enpe/ledterne/media/ledterne-test-display-01.jpg

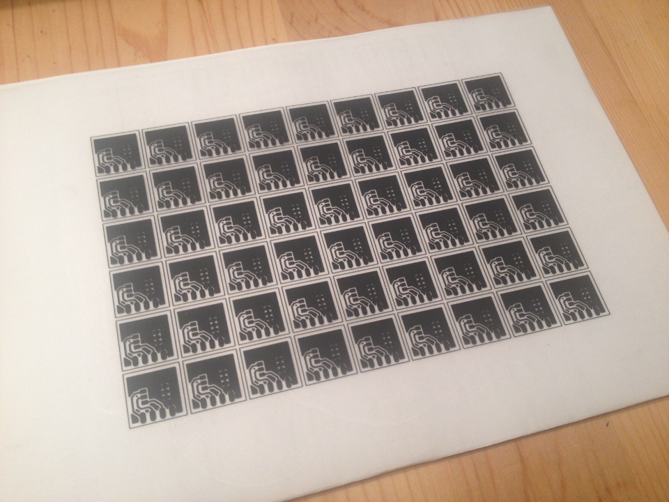
media/ledterne-test-display-01.jpg
