enpe/ledterne/media/ledterne-test-display-03.jpg

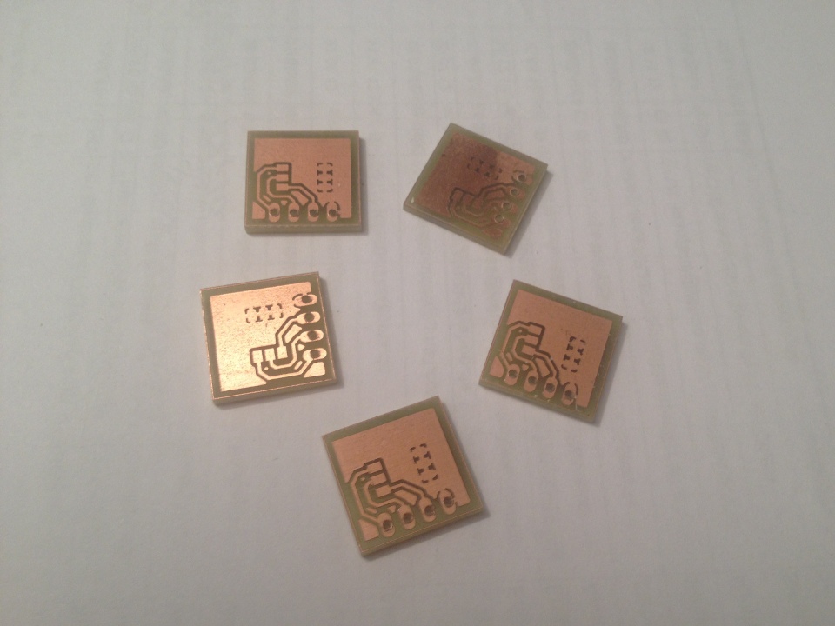
media/ledterne-test-display-03.jpg
