enpe/ledterne/media/ledterne-test-display-06.jpg

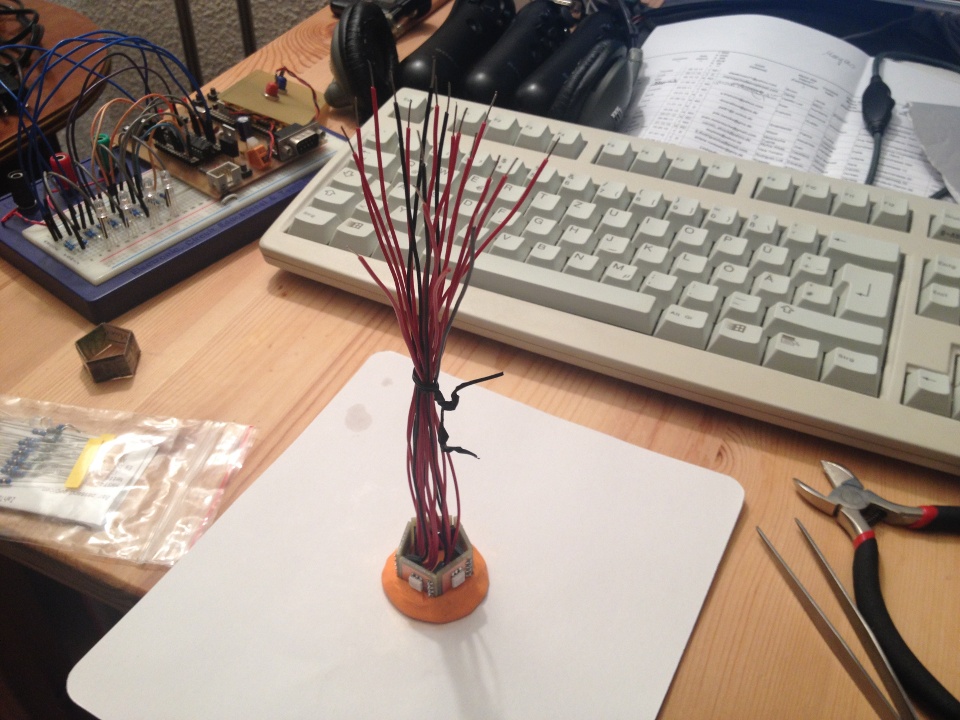
media/ledterne-test-display-06.jpg
