enpe/ledterne/media/ledterne-test-display-07.jpg

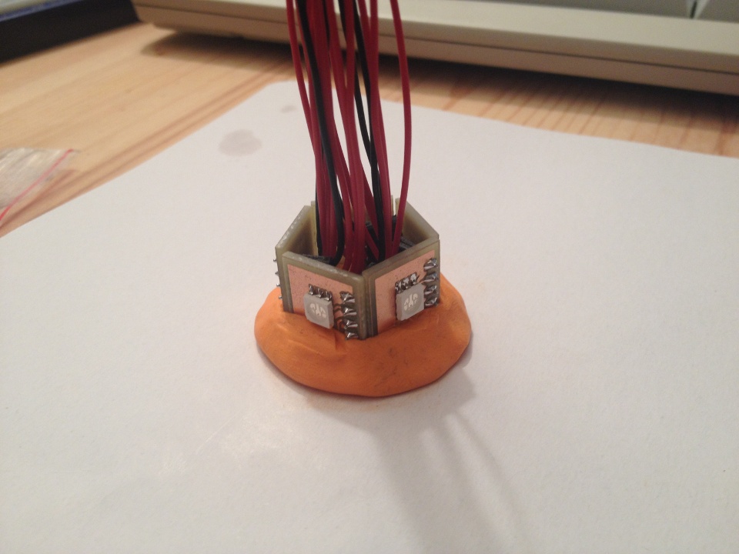
media/ledterne-test-display-07.jpg
