enpe/ledterne/media/ledterne-test-display-08.jpg

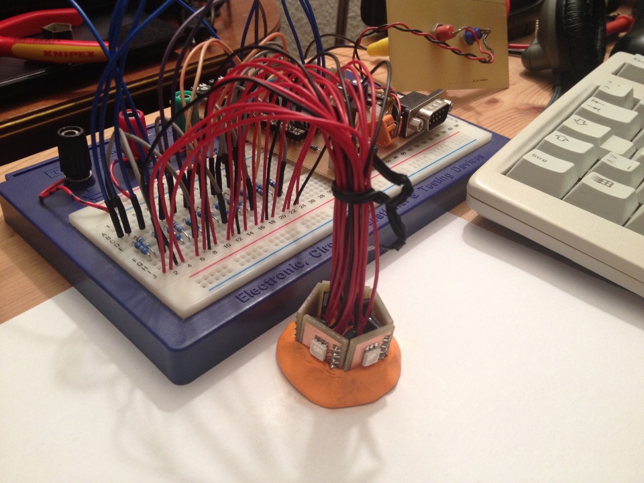
media/ledterne-test-display-08.jpg
