enpe/ledterne/media/ledterne-test-display-10.jpg

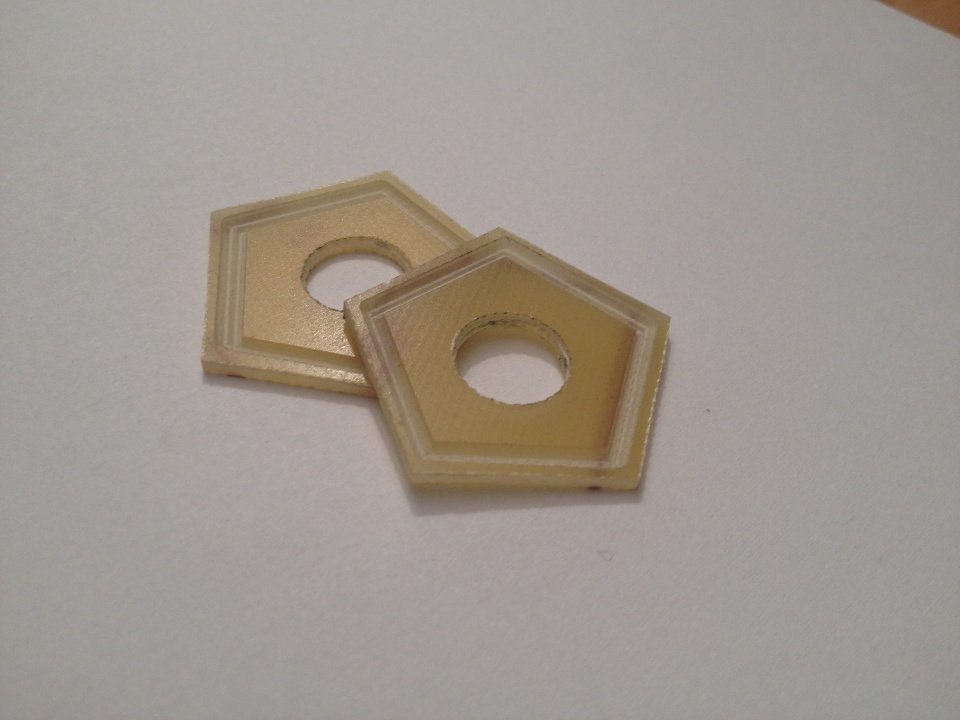
media/ledterne-test-display-10.jpg
